rosmo/spaceballs-switch/main/main.h

#include "esp_zigbee_core.h"

// Button trigger ranges
typedef struct _trigger_range {
    int  min;
    int  max;
    int  button;
    char *name;
} trigger_range;

/* Zigbee configuration */
#define MAX_CHILDREN                    10          /* the max amount of connected devices */
#define INSTALLCODE_POLICY_ENABLE       false    /* enable the install code policy for security */
#define HA_ONOFF_SWITCH_ENDPOINT        1          /* esp light switch device endpoint */
//#define ESP_ZB_PRIMARY_CHANNEL_MASK     ESP_ZB_TRANSCEIVER_ALL_CHANNELS_MASK  /* Zigbee primary channel mask use in the example */
#define ESP_ZB_PRIMARY_CHANNEL_MASK     ESP_ZB_TRANSCEIVER_ALL_CHANNELS_MASK
#define ESP_ZB_SECONDARY_CHANNEL_MASK   ESP_ZB_TRANSCEIVER_ALL_CHANNELS_MASK

#define ESP_ZB_ZR_CONFIG()                                                              \
    {                                                                                   \
        .esp_zb_role = ESP_ZB_DEVICE_TYPE_ROUTER,                                       \
        .install_code_policy = INSTALLCODE_POLICY_ENABLE,                               \
        .nwk_cfg.zczr_cfg = {                                                           \
            .max_children = MAX_CHILDREN,                                               \
        },                                                                              \
    }

#define ED_AGING_TIMEOUT                ESP_ZB_ED_AGING_TIMEOUT_64MIN
#define ED_KEEP_ALIVE                   3000    /* 3000 millisecond */
#define ESP_ZB_ZED_CONFIG()                                         \
    {                                                               \
        .esp_zb_role = ESP_ZB_DEVICE_TYPE_ED,                       \
        .install_code_policy = INSTALLCODE_POLICY_ENABLE,           \
        .nwk_cfg.zed_cfg = {                                        \
            .ed_timeout = ED_AGING_TIMEOUT,                         \
            .keep_alive = ED_KEEP_ALIVE,                            \
        },                                                          \
    }

#define ESP_ZB_DEFAULT_RADIO_CONFIG()                           \
    {                                                           \
        .radio_mode = ZB_RADIO_MODE_NATIVE,                        \
    }

#define ESP_ZB_DEFAULT_HOST_CONFIG()                            \
    {                                                           \
        .host_connection_mode = ZB_HOST_CONNECTION_MODE_NONE,      \
    }
